cmsegiet/nixieclock/Simulation/Draft2.asc

C1: cap; 0.1µf
C2: cap; 100pF
R1: res; 22k
R2: res; 22k
R3: res; 1k
U1: opamp2; OPA2344
V1: voltage; 5V
V2: voltage; 200mV
Named nets: 0, V+, vout
.inc opa2344.lib
.tran 0 100ms 0 20ms startup
